HalFrgrd/SplitKeyboard/3DPrinting/microcontrollerholder.stl

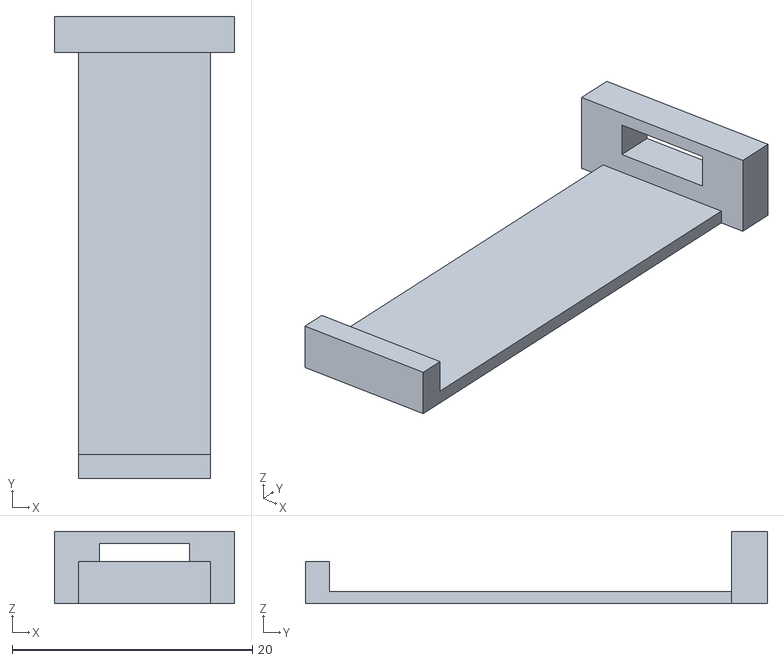
[picture p28: CAD file, 2017-06-07]
3DPrinting/microcontrollerholder.stl
15.0 x 38.5 x 6.00
