HalFrgrd/SplitKeyboard/hfopt/Untitled-595a0aec.stl

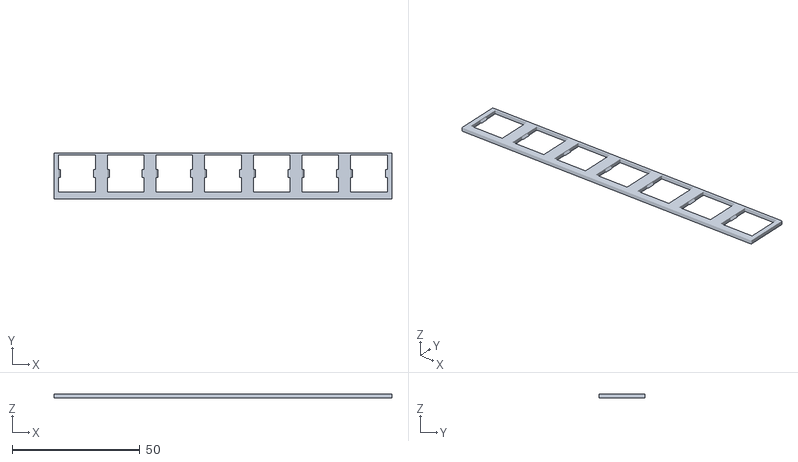
[picture p29: CAD file, 2017-07-06]
hfopt/Untitled-595a0aec.stl
132.3 x 18.0 x 1.50
