HalFrgrd/SplitKeyboard/hfopt/Untitled-59578781.stl

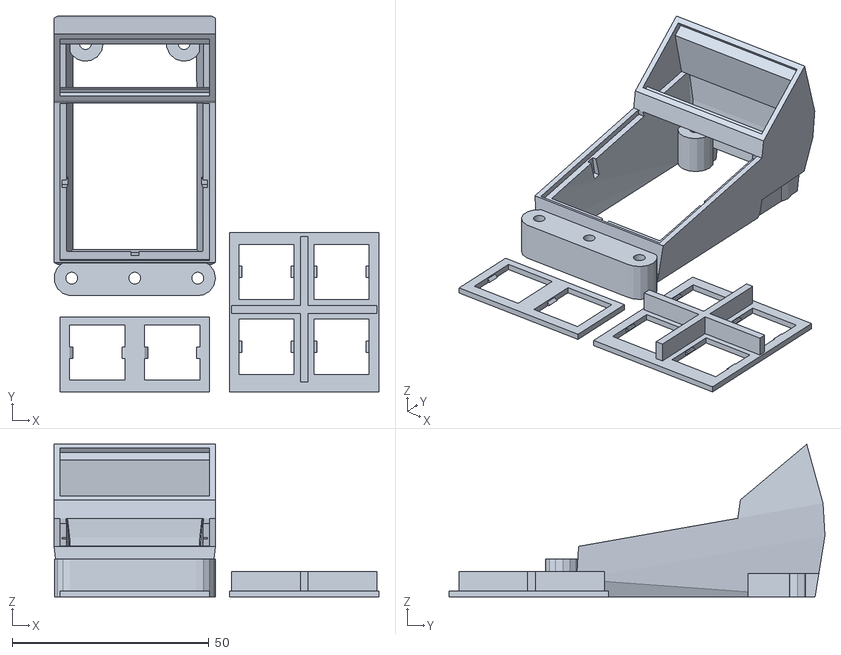
[picture p30: CAD file, 2017-07-06]
hfopt/Untitled-59578781.stl
82.6 x 95.6 x 38.8
