HalFrgrd/SplitKeyboard/hfopt/Untitled-5959ca69.stl

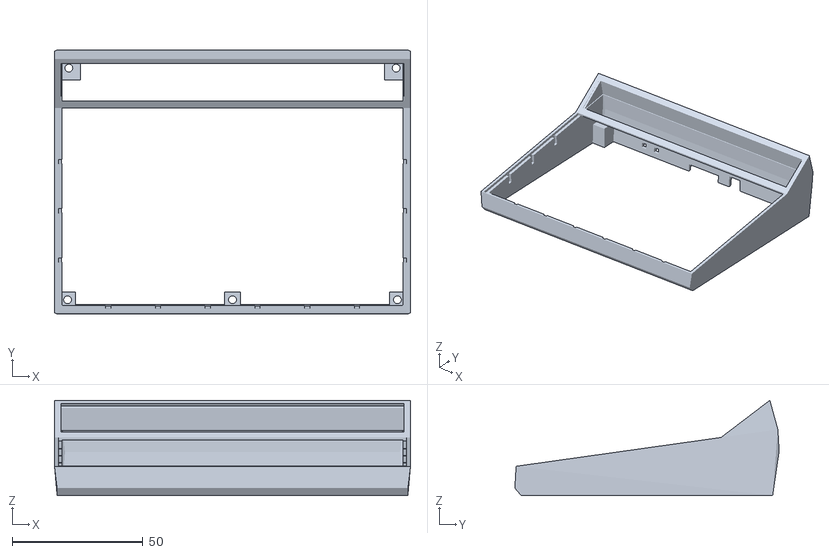
[picture p31: CAD file, 2017-07-06]
hfopt/Untitled-5959ca69.stl
136.3 x 101.2 x 36.5
