HalFrgrd/SplitKeyboard/hfopt/Untitled-5959bd14.stl

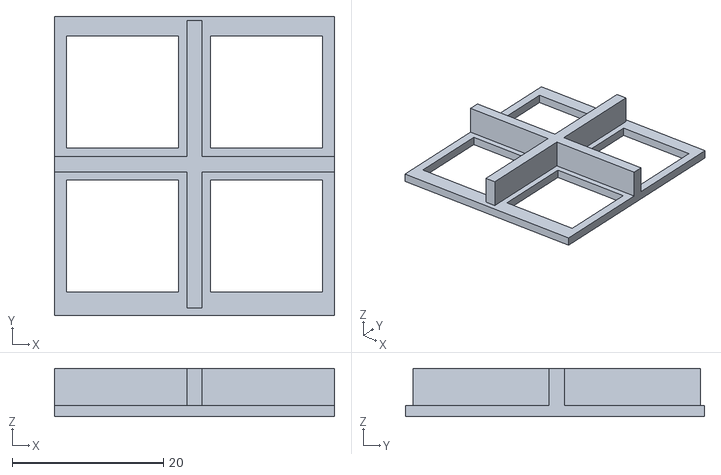
[picture p32: CAD file, 2017-07-06]
hfopt/Untitled-5959bd14.stl
37.0 x 39.6 x 6.40
