HalFrgrd/SplitKeyboard/hfopt/optcase/post-demo.scad

union () {
  cube ([100, 100, 100], center=true);
  sphere (r=110);
  cylinder (h=150, r=10, center=true);
}
